anchit92/ESP32-RaceBox-mini-Emulator/Mods/anchit92/Battery_version/STL/Lid HGLRC M100-5883 gps.3mf

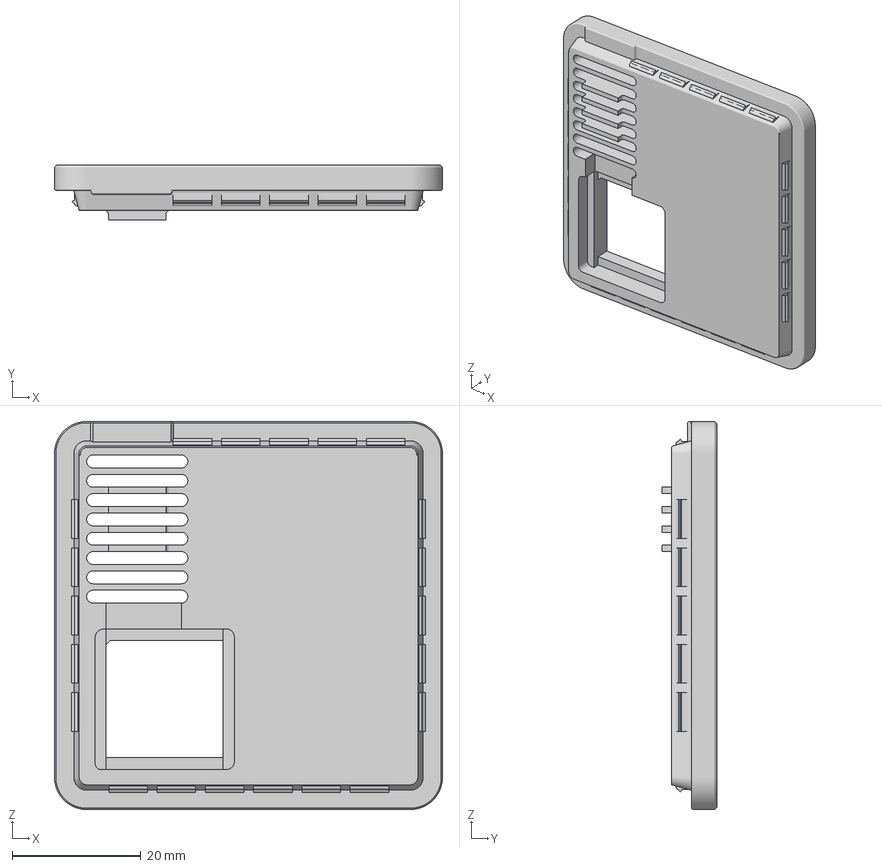
[picture p27: CAD file, 2026-02-03]
Mods/anchit92/Battery_version/STL/Lid HGLRC M100-5883 gps.3mf
60.3 x 8.59 x 60.3 mm
