anchit92/ESP32-RaceBox-mini-Emulator/Mods/anchit92/PCB_version/STL/Lid.3mf

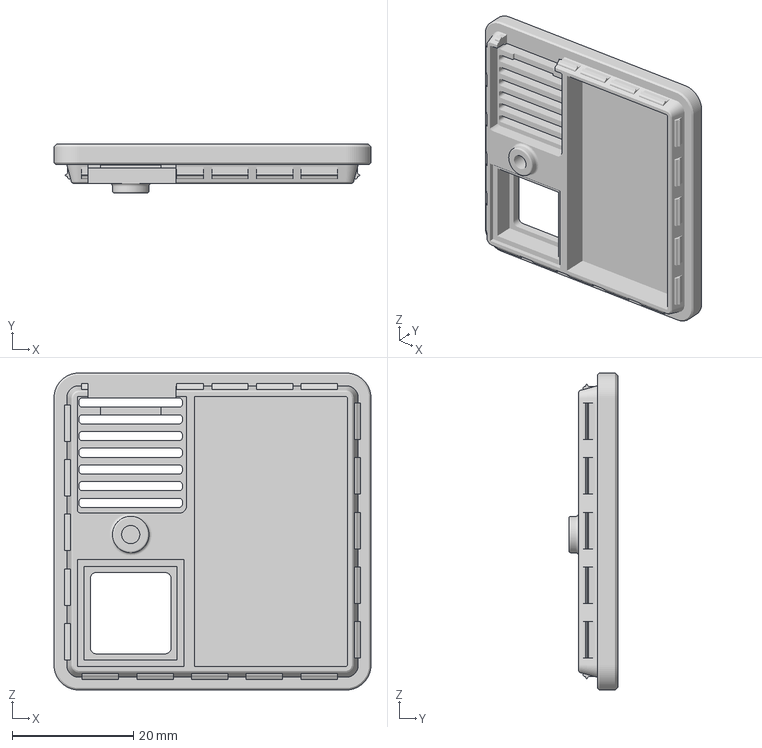
[picture p30: CAD file, 2026-03-14]
Mods/anchit92/PCB_version/STL/Lid.3mf
52.2 x 8.10 x 52.2 mm
