anchit92/ESP32-RaceBox-mini-Emulator/Mods/anchit92/Battery_version/STL/Lid MG-903 gps.3mf

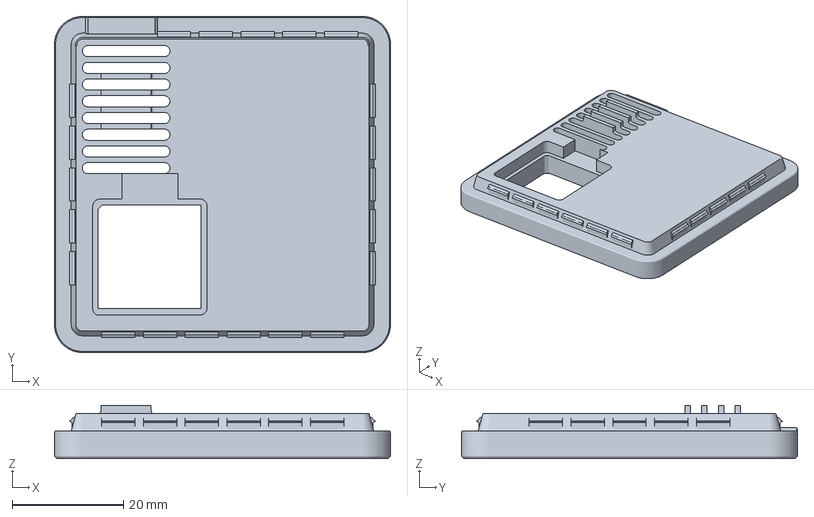
[picture p31: CAD file, 2026-02-01]
Mods/anchit92/Battery_version/STL/Lid MG-903 gps.3mf
60.3 x 60.3 x 9.59 mm
