anchit92/ESP32-RaceBox-mini-Emulator/Mods/anchit92/PCB_version/STL/GoPro Base.3mf

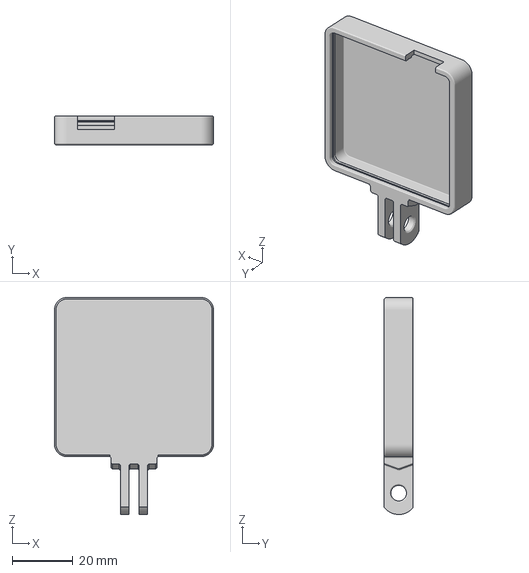
[picture p32: CAD file, 2026-03-14]
Mods/anchit92/PCB_version/STL/GoPro Base.3mf
52.2 x 9.50 x 71.2 mm
