anchit92/ESP32-RaceBox-mini-Emulator/Mods/anchit92/Battery_version/STL/Lid SAM-M10Q gps.3mf

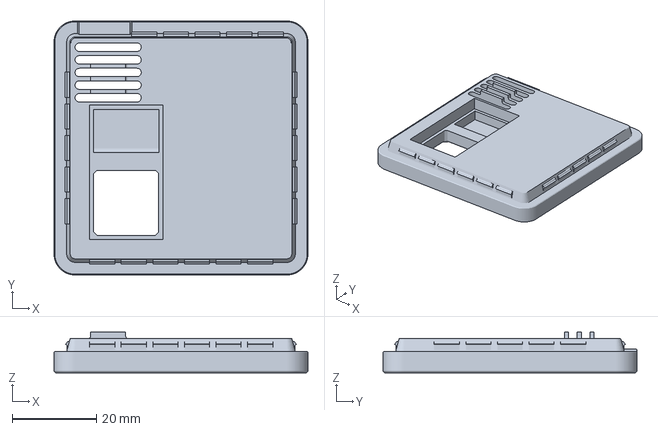
[picture p33: CAD file, 2026-02-01]
Mods/anchit92/Battery_version/STL/Lid SAM-M10Q gps.3mf
60.3 x 60.3 x 9.69 mm
