anchit92/ESP32-RaceBox-mini-Emulator/Mods/anchit92/PCB_version/STL/Base.3mf

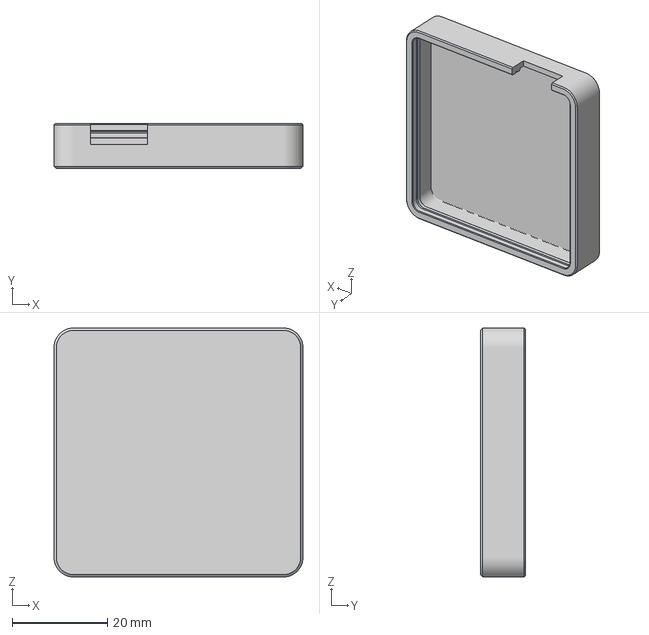
[picture p34: CAD file, 2026-03-14]
Mods/anchit92/PCB_version/STL/Base.3mf
52.2 x 9.50 x 52.2 mm
