anchit92/ESP32-RaceBox-mini-Emulator/STL/Lids/Lid_SAM-M10Q_GPS.3mf

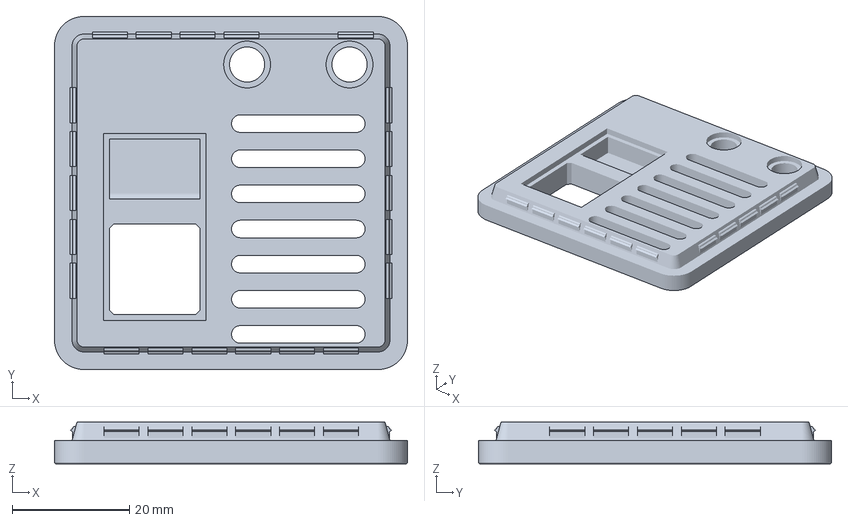
[picture p35: CAD file, 2025-06-12]
STL/Lids/Lid_SAM-M10Q_GPS.3mf
60.3 x 60.3 x 7.10 mm
